dtomcat/XP-chip/images/bitbus2flash.png

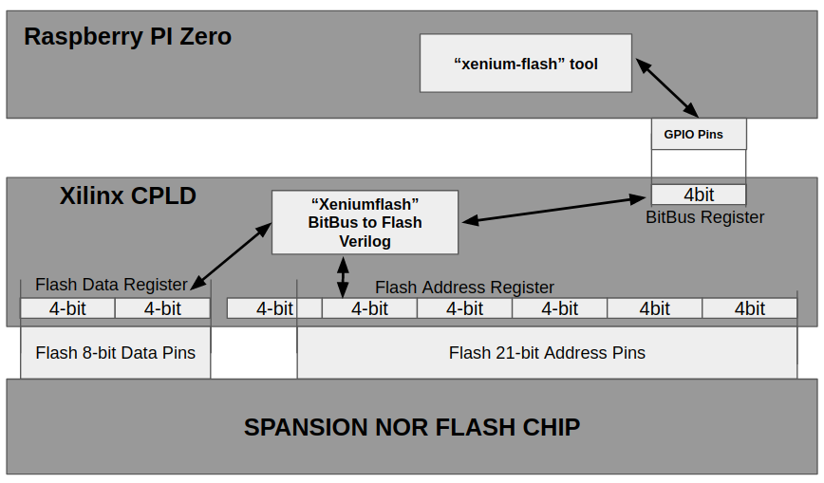
images/bitbus2flash.png
