dtomcat/XP-chip/images/bitbus.png

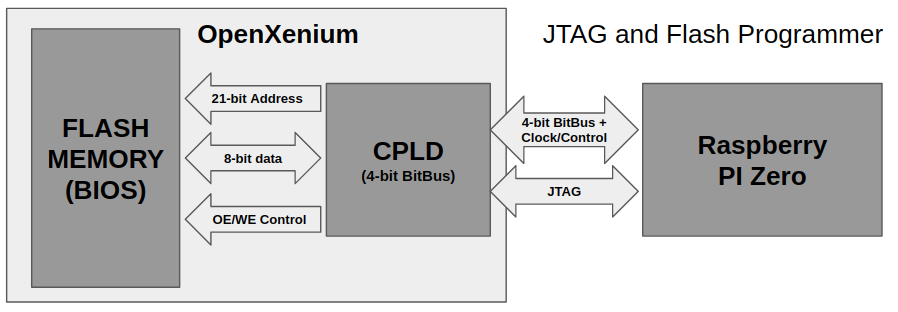
images/bitbus.png
