dtomcat/XP-chip/images/boot.png

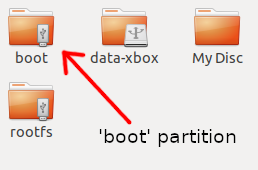
images/boot.png
