dtomcat/XP-chip/images/connections-omega.png

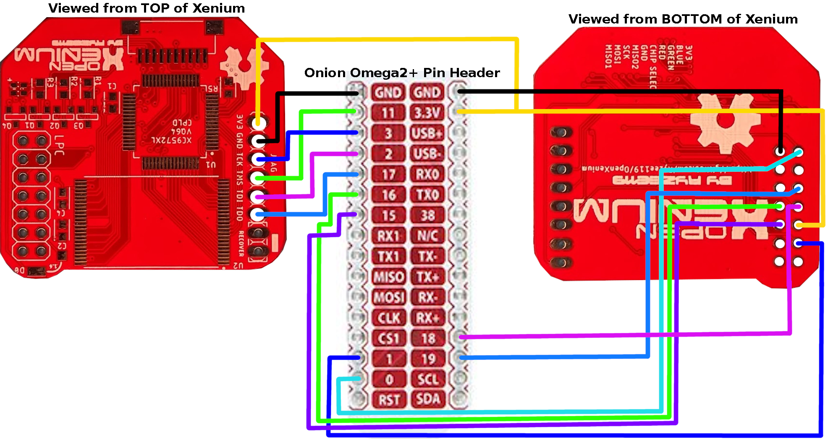
images/connections-omega.png
