dtomcat/XP-chip/images/connections-pi.png

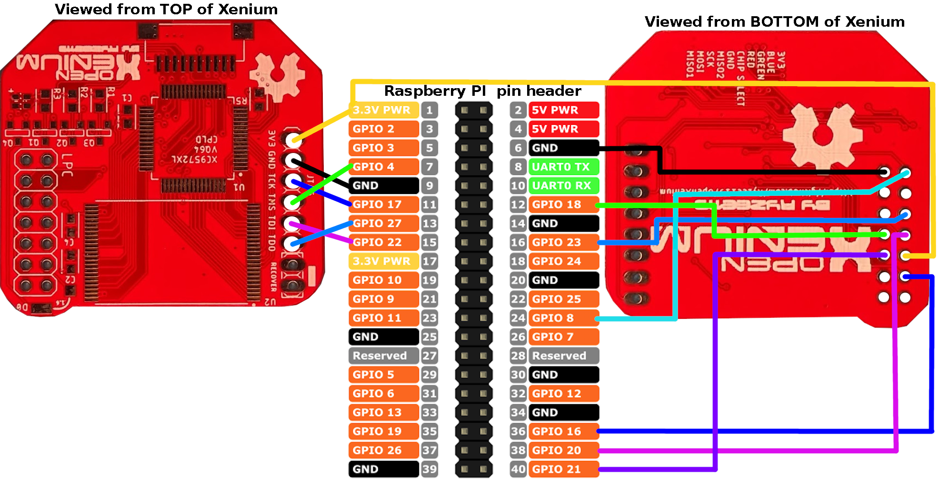
images/connections-pi.png
