dtomcat/XP-chip/images/five-bucks.png

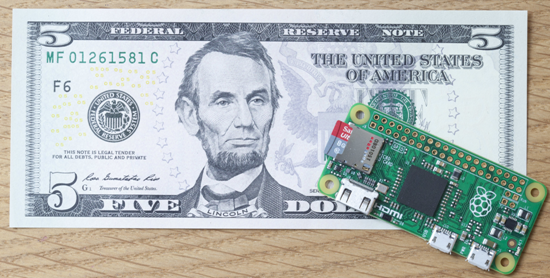
images/five-bucks.png
