dtomcat/XP-chip/images/lpc-bus.png

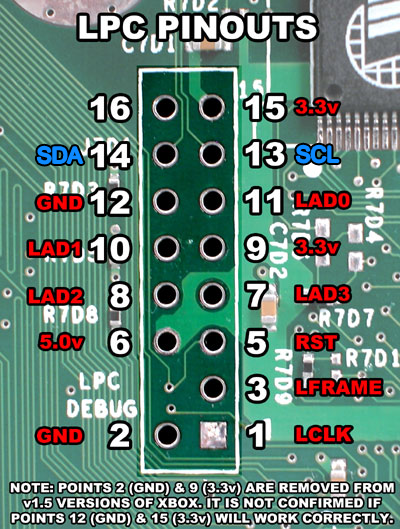
images/lpc-bus.png
