dtomcat/XP-chip/images/mcpx-lpc.png

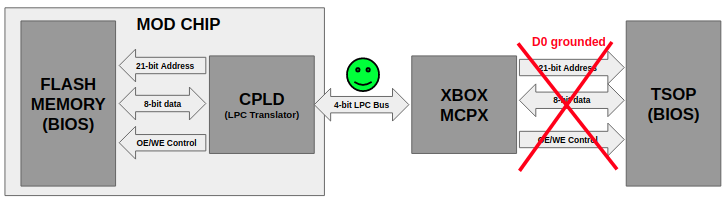
images/mcpx-lpc.png
