dtomcat/XP-chip/images/openxenium2.jpg

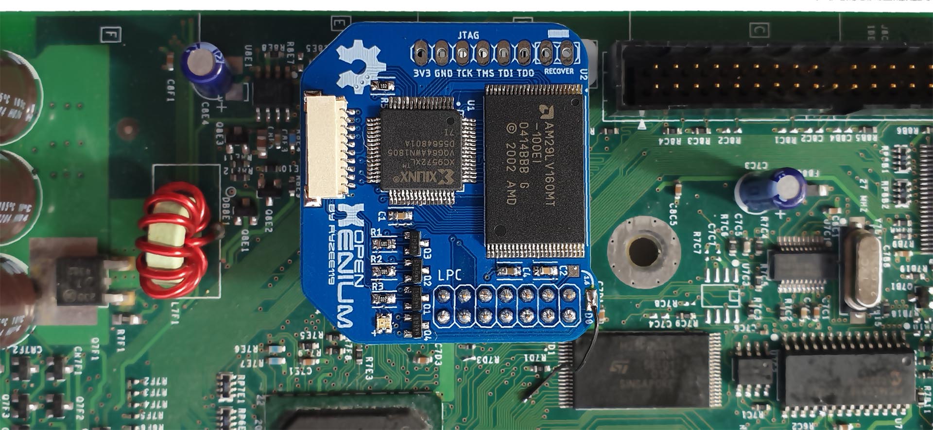
images/openxenium2.jpg
