dtomcat/XP-chip/images/openxenium.jpg

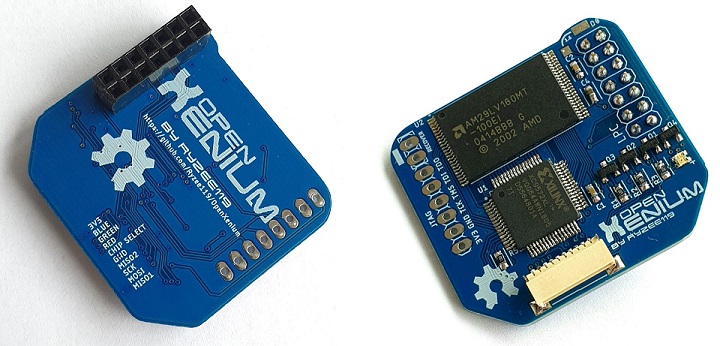
images/openxenium.jpg
