dtomcat/XP-chip/images/pi-spi.jpg

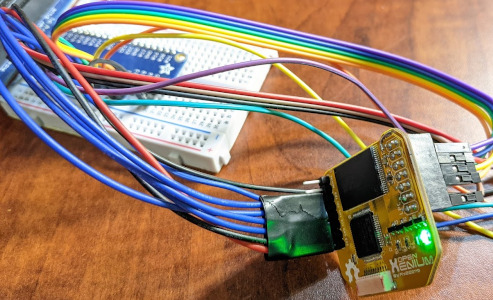
images/pi-spi.jpg
