dtomcat/XP-chip/images/pi-wifi.png

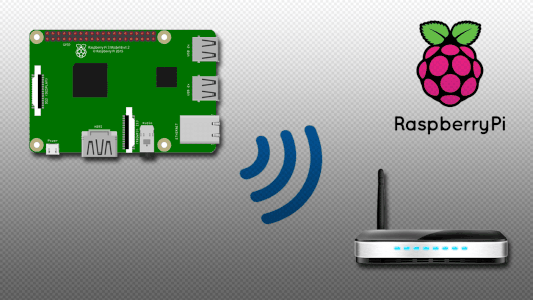
images/pi-wifi.png
