dtomcat/XP-chip/images/pinout-omega.png

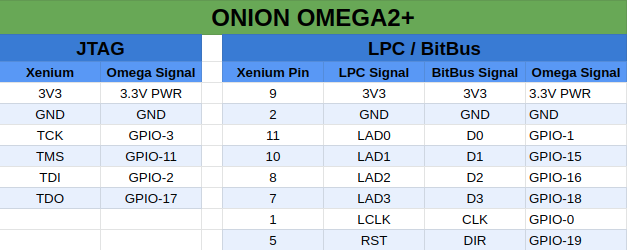
images/pinout-omega.png
