dtomcat/XP-chip/images/pinout-pi.png

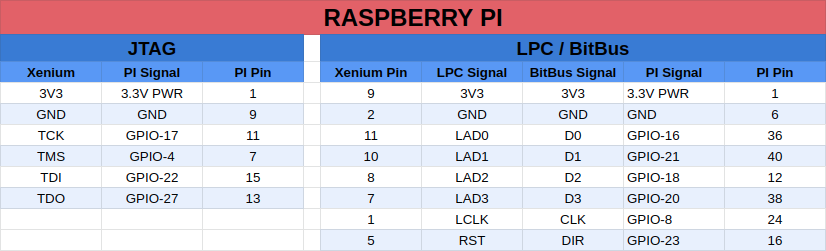
images/pinout-pi.png
