dtomcat/XP-chip/images/xenium-os.jpg

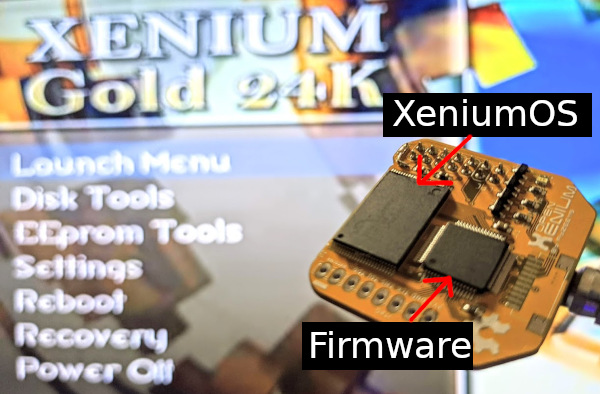
images/xenium-os.jpg
