dtomcat/XP-chip/images/xilinx-programmer.jpg

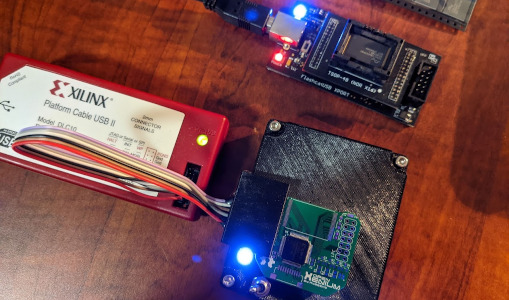
images/xilinx-programmer.jpg
