dtomcat/XP-chip/xenium-flash/src/flash/BitBus.cpp

/* Custom 4-bit "BitBus"

Copyright (C) 2019-2020 Koos du Preez (kdupreez@hotmail.com)

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
You should have received a copy of the GNU General Public License
along with this program; if not, write to the Free Software
Foundation, Inc., 59 Temple Place, Suite 330, Boston, MA  02111-1307  USA
*/

#include "BitBus.hpp"

#include <thread>
#include <chrono>

#include "XeniumDefines.h"

namespace XK
{
    BitBus::BitBus()
    { }

    void BitBus::SetPlatformDelay(bool delay_enabled)
    {
        platform_delay_ = delay_enabled;
    }
}
